okayumoka/mysplit/picture/IMG_20180529_205150.jpg

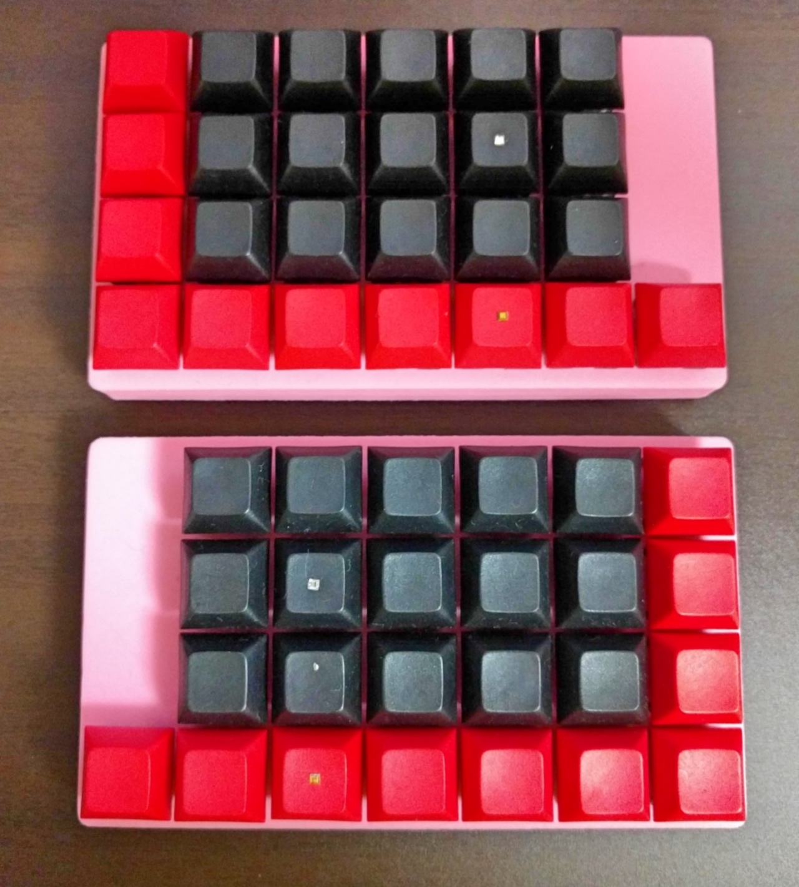
picture/IMG_20180529_205150.jpg
