okayumoka/mysplit/picture/IMG_20180529_205200.jpg

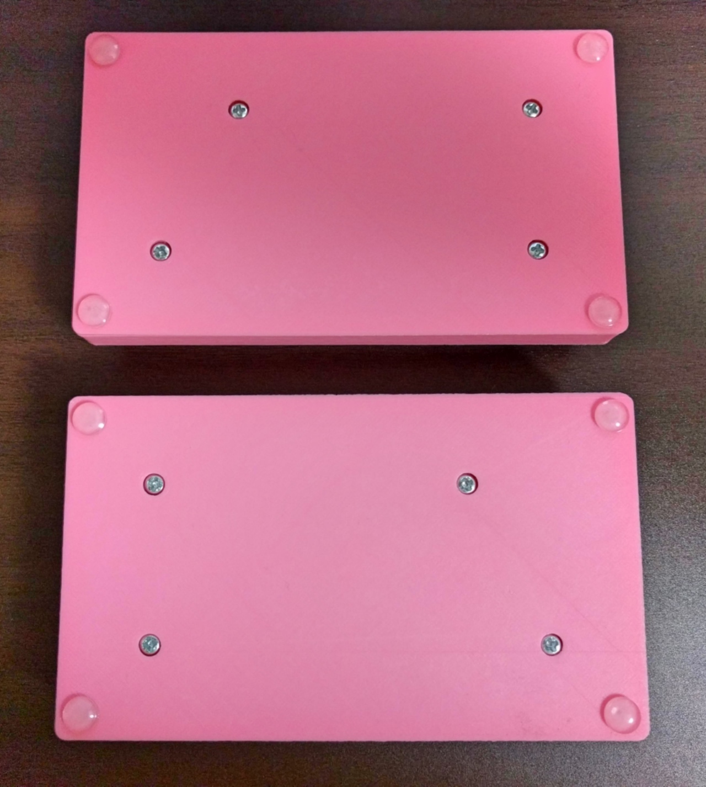
picture/IMG_20180529_205200.jpg
