okayumoka/mysplit/picture/IMG_20180529_205521.jpg

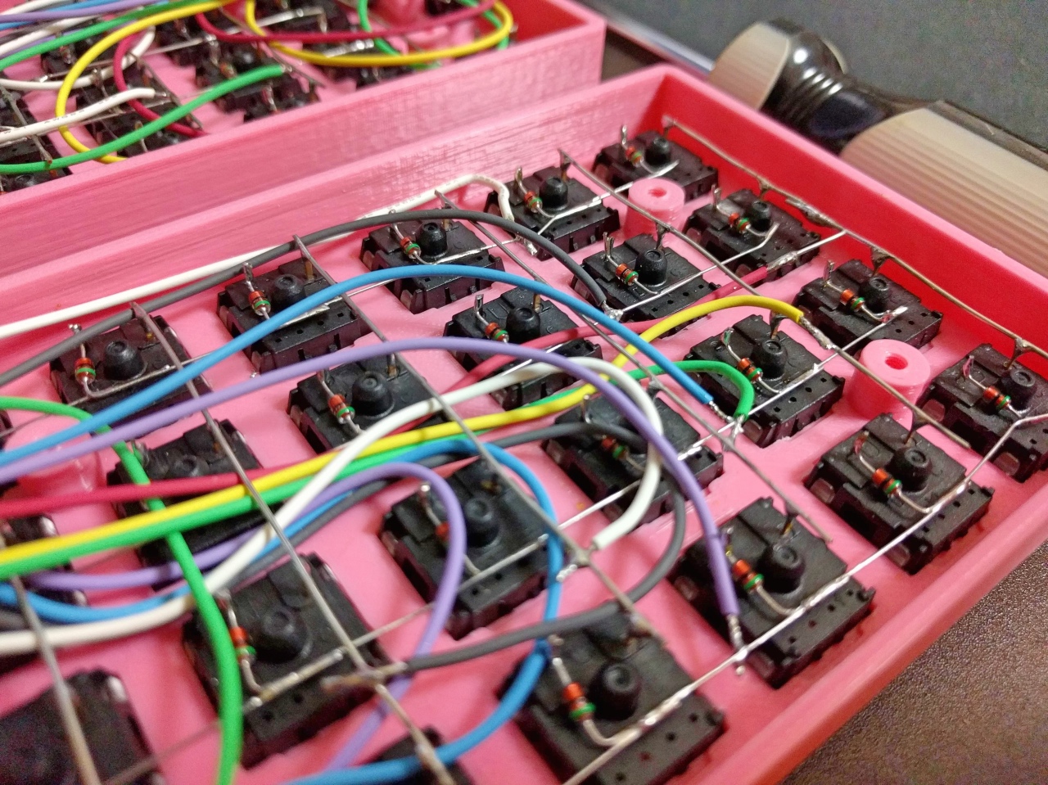
picture/IMG_20180529_205521.jpg
