okayumoka/mysplit/picture/IMG_20180529_211748.jpg

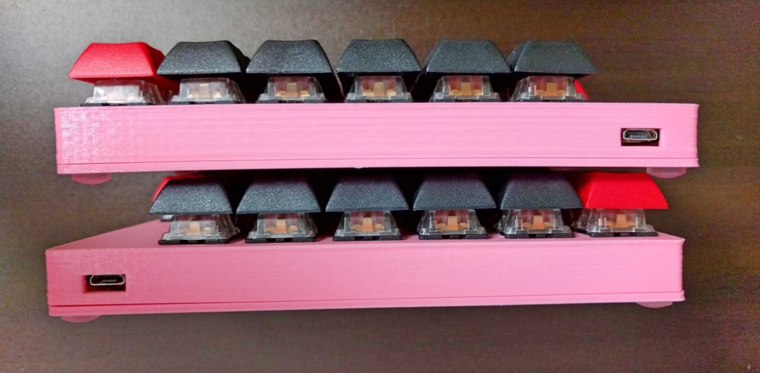
picture/IMG_20180529_211748.jpg
