okayumoka/mysplit/picture/IMG_20180529_211849.jpg

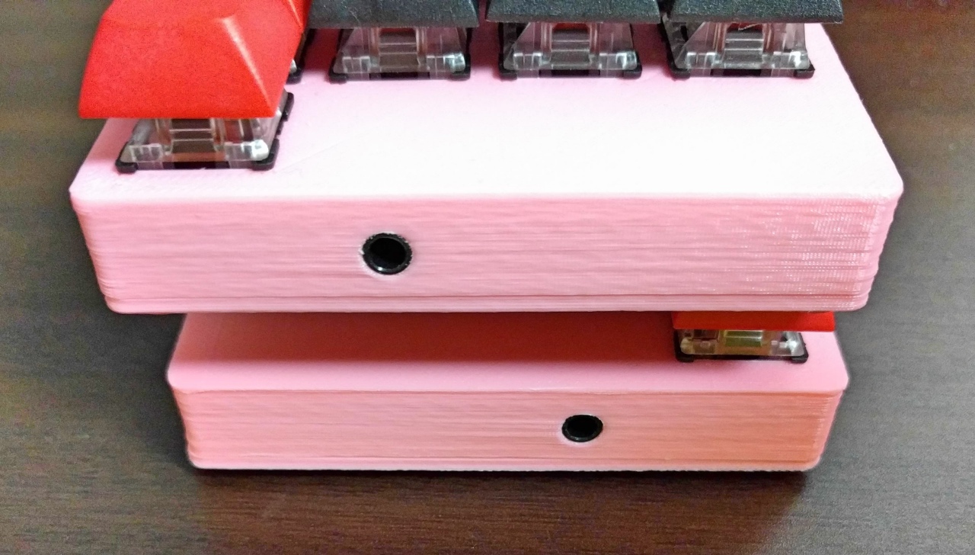
picture/IMG_20180529_211849.jpg
