okayumoka/mysplit/firmware/mysplit/keycode.h

#ifndef __INCLUDED_KEYCODE_H__
#define __INCLUDED_KEYCODE_H__

#define KC_NULL 0x00
#define KC_SOH 0x01
#define KC_STX 0x02
#define KC_ETX 0x03
#define KC_EOT 0x04
#define KC_ENQ 0x05
#define KC_ACK 0x06
#define KC_BEL 0x07
#define KC_BS 0x08
#define KC_TAB 0x09
#define KC_LF 0x0A
#define KC_VTAB 0x0B
#define KC_FF 0x0C
#define KC_CR 0x0D
#define KC_SO 0x0E
#define KC_SI 0x0F
#define KC_DLE 0x10
#define KC_DC1 0x11
#define KC_DC2 0x12
#define KC_DC3 0x13
#define KC_DC4 0x14
#define KC_NAK 0x15
#define KC_SYN 0x16
#define KC_ETB 0x17
#define KC_CAN 0x18
#define KC_EM 0x19
#define KC_SUB 0x1A
#define KC_ESC 0x1B
#define KC_FS 0x1C
#define KC_GS 0x1D
#define KC_RS 0x1E
#define KC_US 0x1F
#define KC_SPC 0x20
#define KC_EXLM 0x21
#define KC_DQUO 0x22
#define KC_HASH 0x23
#define KC_DLR 0x24
#define KC_PERC 0x25
#define KC_AMP 0x26
#define KC_QUOT 0x27
#define KC_LPRN 0x28
#define KC_RPRN 0x29
#define KC_ASTR 0x2A
#define KC_PLUS 0x2B
#define KC_COMM 0x2C
#define KC_MINS 0x2D
#define KC_DOT 0x2E
#define KC_SLSH 0x2F
#define KC_0 0x30
#define KC_1 0x31
#define KC_2 0x32
#define KC_3 0x33
#define KC_4 0x34
#define KC_5 0x35
#define KC_6 0x36
#define KC_7 0x37
#define KC_8 0x38
#define KC_9 0x39
#define KC_CLN 0x3A
#define KC_SCLN 0x3B
#define KC_LT 0x3C
#define KC_EQL 0x3D
#define KC_GT 0x3E
#define KC_QUES 0x3F
#define KC_AT 0x40
#define KC_A 0x41
#define KC_B 0x42
#define KC_C 0x43
#define KC_D 0x44
#define KC_E 0x45
#define KC_F 0x46
#define KC_G 0x47
#define KC_H 0x48
#define KC_I 0x49
#define KC_J 0x4A
#define KC_K 0x4B
#define KC_L 0x4C
#define KC_M 0x4D
#define KC_N 0x4E
#define KC_O 0x4F
#define KC_P 0x50
#define KC_Q 0x51
#define KC_R 0x52
#define KC_S 0x53
#define KC_T 0x54
#define KC_U 0x55
#define KC_V 0x56
#define KC_W 0x57
#define KC_X 0x58
#define KC_Y 0x59
#define KC_Z 0x5A
#define KC_LB 0x5B
#define KC_BSLS 0x5C
#define KC_RB 0x5D
#define KC_CRET 0x5E
#define KC_USCR 0x5F
#define KC_GRAV 0x60
#define KC_a 0x61
#define KC_b 0x62
#define KC_c 0x63
#define KC_d 0x64
#define KC_e 0x65
#define KC_f 0x66
#define KC_g 0x67
#define KC_h 0x68
#define KC_i 0x69
#define KC_j 0x6A
#define KC_k 0x6B
#define KC_l 0x6C
#define KC_m 0x6D
#define KC_n 0x6E
#define KC_o 0x6F
#define KC_p 0x70
#define KC_q 0x71
#define KC_r 0x72
#define KC_s 0x73
#define KC_t 0x74
#define KC_u 0x75
#define KC_v 0x76
#define KC_w 0x77
#define KC_x 0x78
#define KC_y 0x79
#define KC_z 0x7A
#define KC_LCB 0x7B
#define KC_VBAR 0x7C
#define KC_RCB 0x7D
#define KC_TILD 0x7E
#define KC_DEL 0x7F
#define KC_LCTL 0x80
#define KC_LSFT 0x81
#define KC_LALT 0x82
#define KC_LGUI 0x83
#define KC_RCTL 0x84
#define KC_RSFT 0x85
#define KC_RALT 0x86
#define KC_RGUI 0x87
#define KC_RET 0xB0
#define KC_ESC 0xB1
#define KC_BS 0xB2
#define KC_TAB 0xB3
#define KC_CAPS 0xC1
#define KC_F1 0xC2
#define KC_F2 0xC3
#define KC_F3 0xC4
#define KC_F4 0xC5
#define KC_F5 0xC6
#define KC_F6 0xC7
#define KC_F7 0xC8
#define KC_F8 0xC9
#define KC_F9 0xCA
#define KC_F10 0xCB
#define KC_F11 0xCC
#define KC_F12 0xCD
#define KC_PSCR 0xCE
#define KC_SCLK 0xCF
#define KC_PAUS 0xD0
#define KC_INS 0xD1
#define KC_HOME 0xD2
#define KC_PGUP 0xD3
#define KC_DEL 0xD4
#define KC_END 0xD5
#define KC_PGDN 0xD6
#define KC_RGHT 0xD7
#define KC_LEFT 0xD8
#define KC_DOWN 0xD9
#define KC_UP 0xDA
#define KC_NLOC 0xE0
#define KC_F13 0xF0
#define KC_F14 0xF1
#define KC_F15 0xF2
#define KC_F16 0xF3
#define KC_F17 0xF4
#define KC_F18 0xF5
#define KC_F19 0xF6
#define KC_F20 0xF7
#define KC_F21 0xF8
#define KC_F22 0xF9
#define KC_F23 0xFA
#define KC_F24 0xFB
#define KC_MENU 0xFE
#define KC_RISE 0x100
#define KC_LOWR 0x101
#define KC_CTSP 0x102

#endif
